VCF/3DStreetNumbers/Z.stl

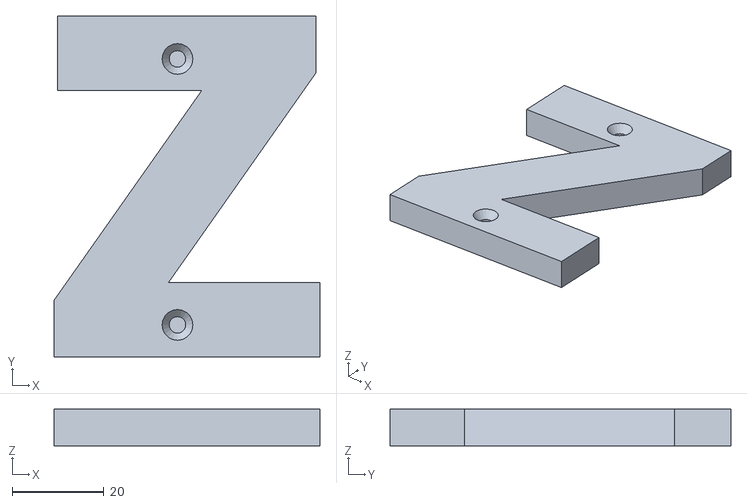
[picture p16: CAD file, 2019-05-19]
Z.stl
57.9 x 74.4 x 8.00
