VCF/3DStreetNumbers/O.stl

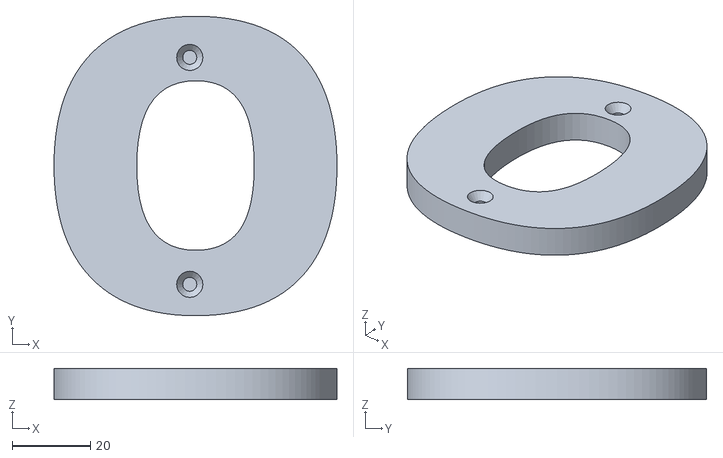
[picture p17: CAD file, 2019-05-19]
O.stl
72.3 x 76.5 x 8.00
