VCF/3DStreetNumbers/U.stl

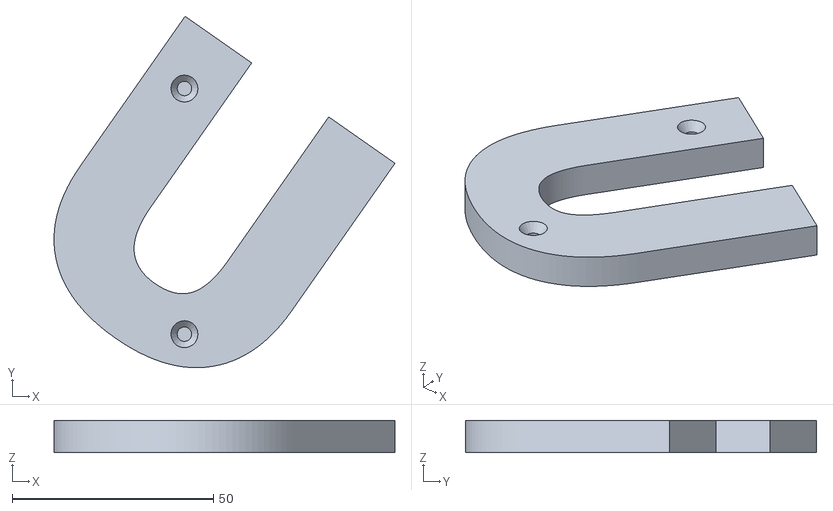
[picture p18: CAD file, 2019-05-19]
U.stl
84.7 x 87.3 x 8.00
