VCF/3DStreetNumbers/num.stl

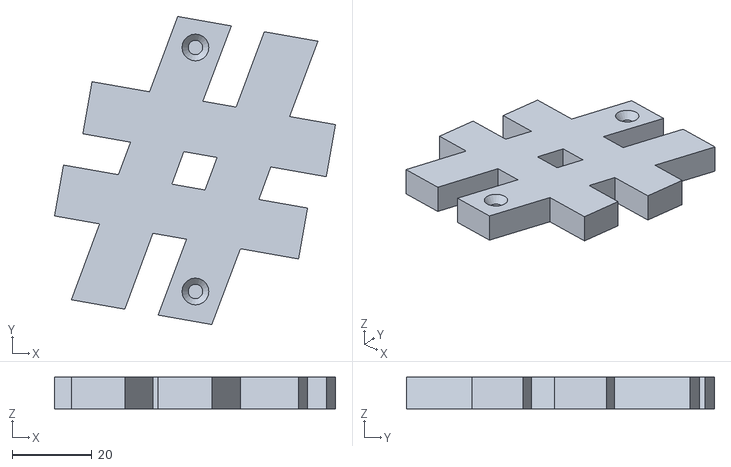
[picture p19: CAD file, 2019-05-19]
num.stl
70.3 x 77.0 x 8.00
