VCF/3DStreetNumbers/dot.stl

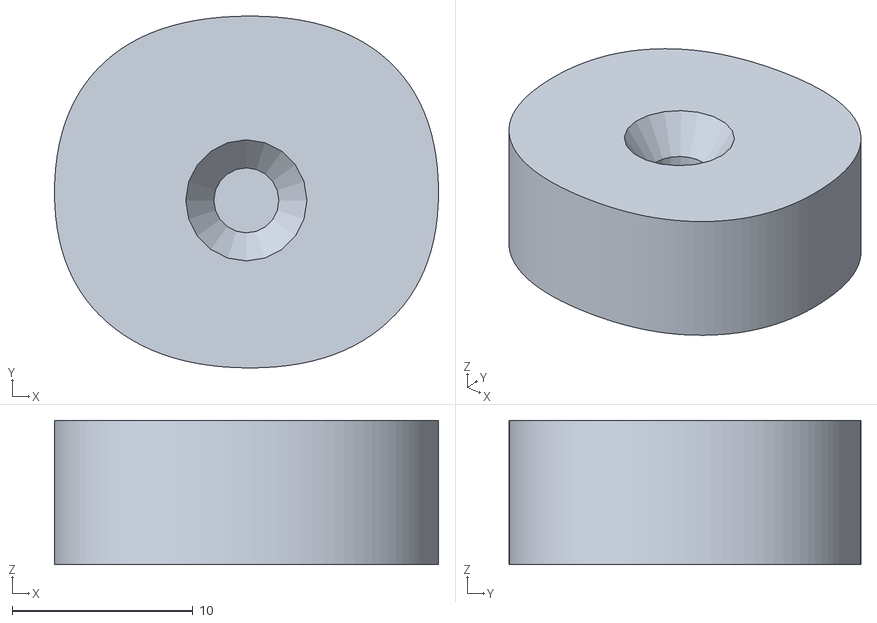
[picture p20: CAD file, 2019-05-18]
dot.stl
21.3 x 19.5 x 8.00
