VCF/3DStreetNumbers/F.stl

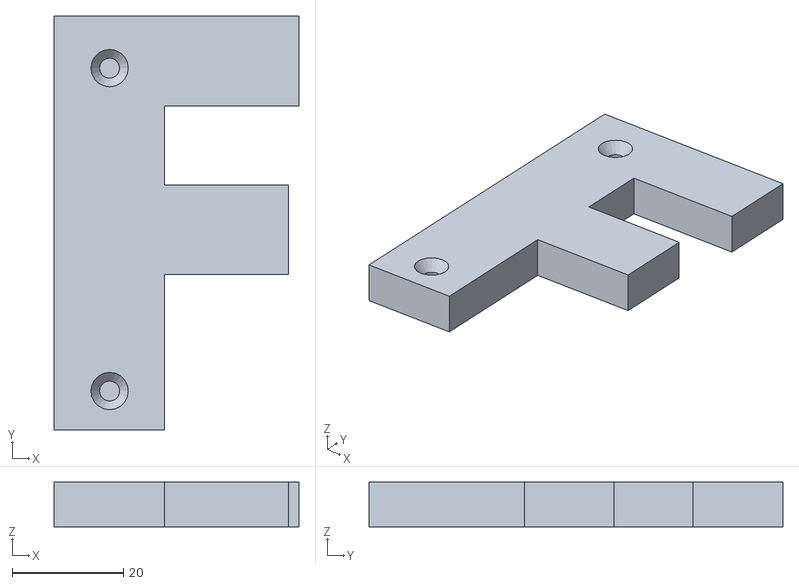
[picture p21: CAD file, 2019-05-18]
F.stl
44.0 x 74.4 x 8.00
