VCF/3DStreetNumbers/A.stl

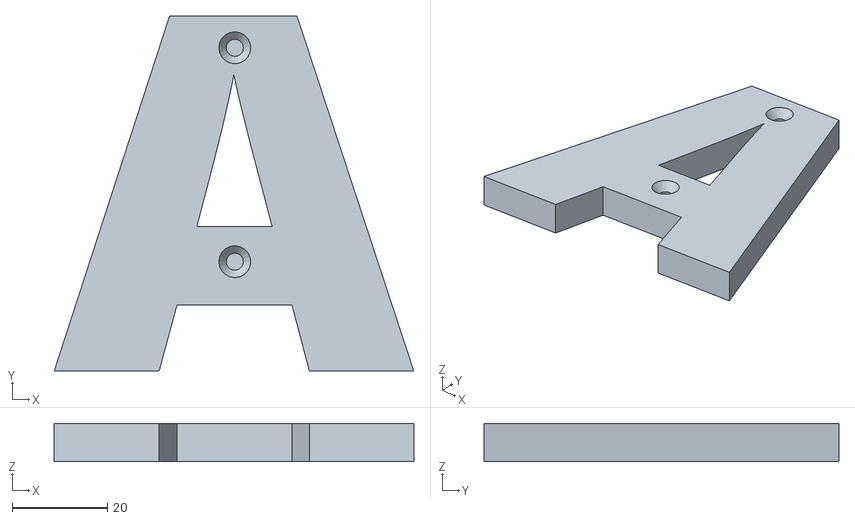
[picture p22: CAD file, 2019-05-18]
A.stl
75.7 x 74.7 x 8.00
