VCF/3DStreetNumbers/B.stl

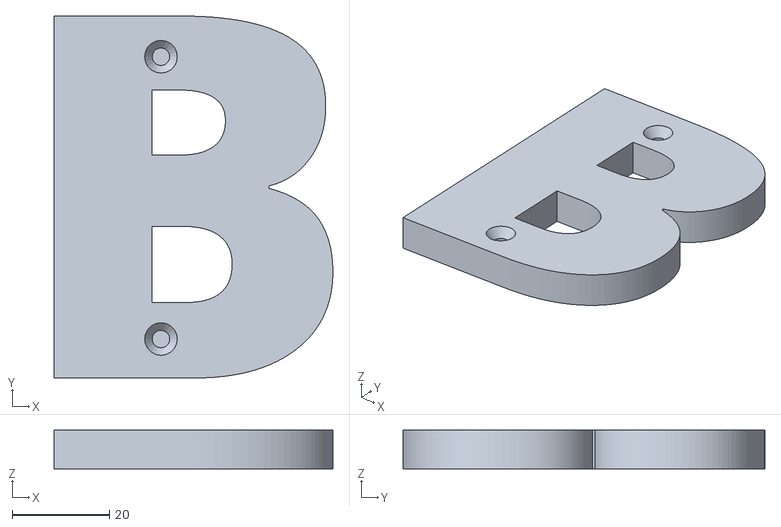
[picture p23: CAD file, 2019-05-18]
B.stl
57.3 x 74.4 x 8.00
