VCF/3DStreetNumbers/dash.stl

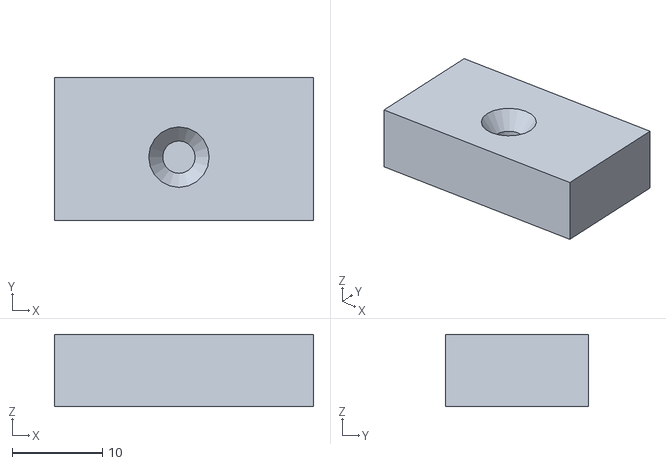
[picture p24: CAD file, 2019-05-18]
dash.stl
28.7 x 15.9 x 8.00
