VCF/3DStreetNumbers/J.stl

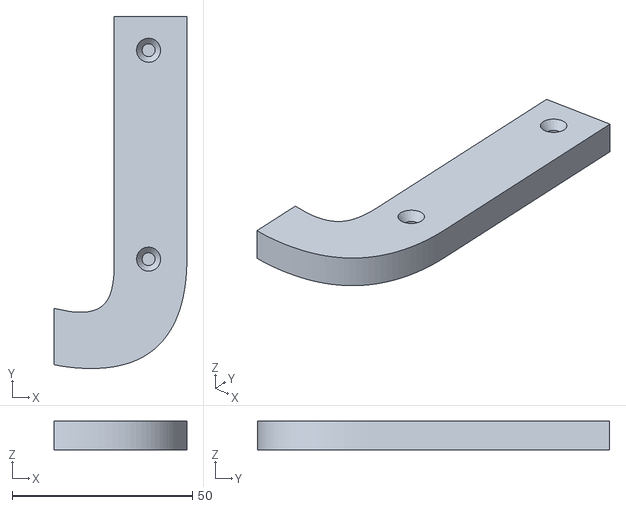
[picture p25: CAD file, 2019-05-18]
J.stl
36.9 x 97.7 x 8.00
