VCF/3DStreetNumbers/H.stl

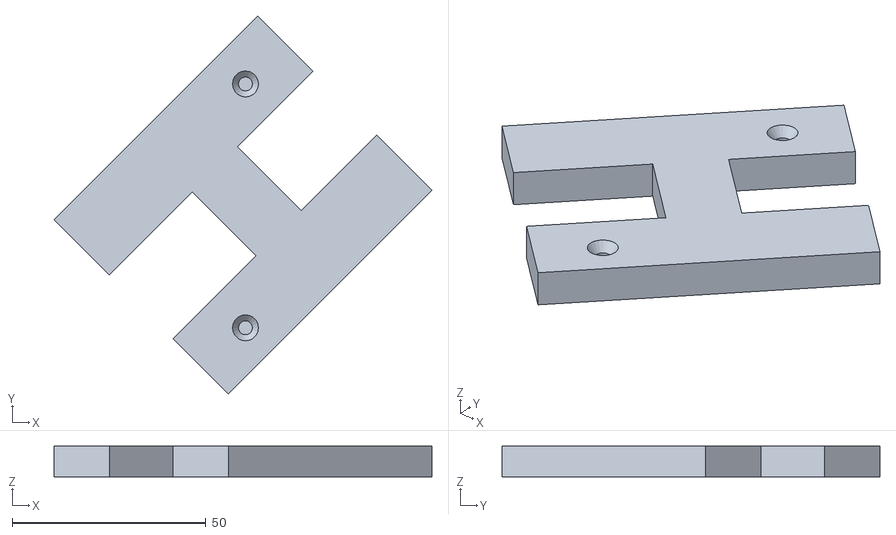
[picture p26: CAD file, 2019-05-18]
H.stl
97.7 x 97.7 x 8.00
