VCF/3DStreetNumbers/C.stl

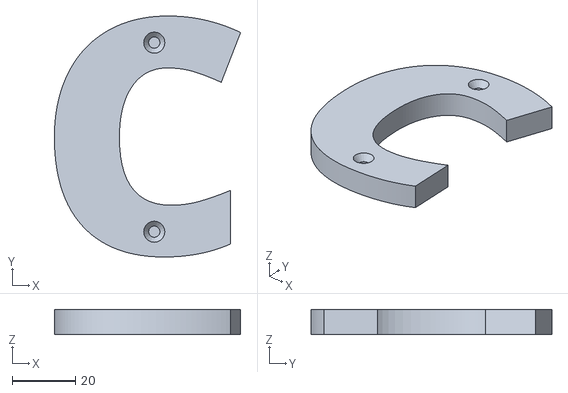
[picture p27: CAD file, 2019-05-18]
C.stl
59.1 x 76.5 x 8.00
