VCF/3DStreetNumbers/K.stl

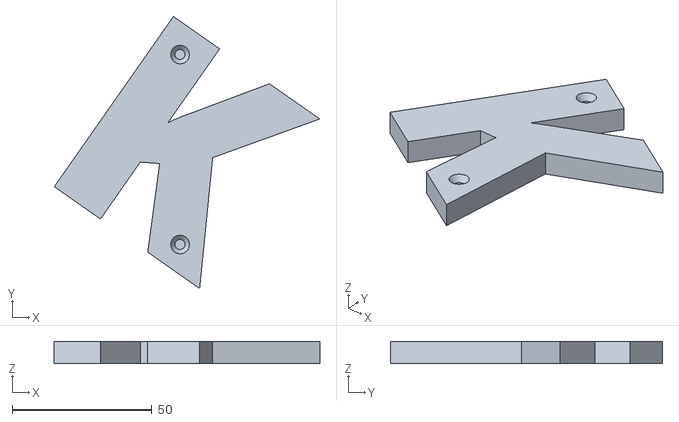
[picture p28: CAD file, 2019-05-18]
K.stl
95.0 x 97.4 x 8.00
