VCF/3DStreetNumbers/and.stl

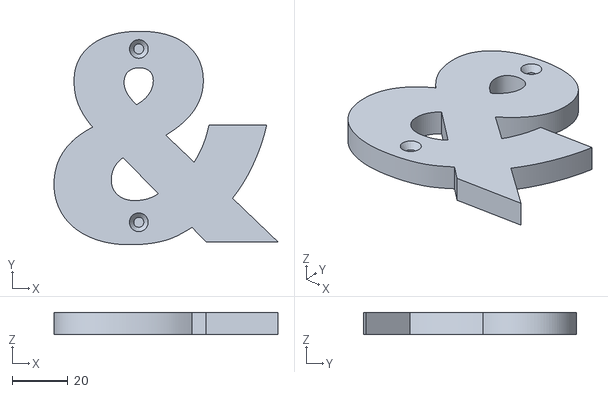
[picture p29: CAD file, 2019-05-18]
and.stl
80.1 x 76.4 x 8.00
