VCF/3DStreetNumbers/E.stl

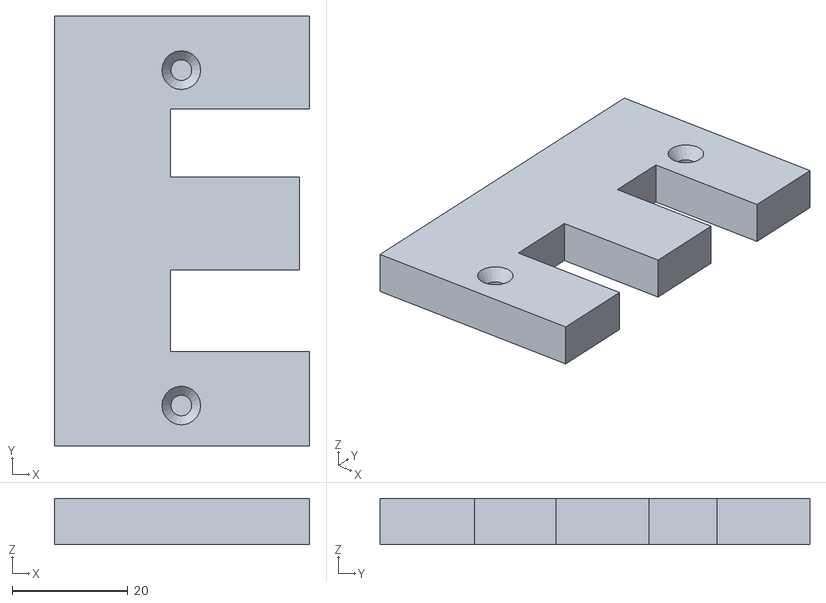
[picture p30: CAD file, 2019-05-18]
E.stl
44.2 x 74.4 x 8.00
