VCF/3DStreetNumbers/I.stl

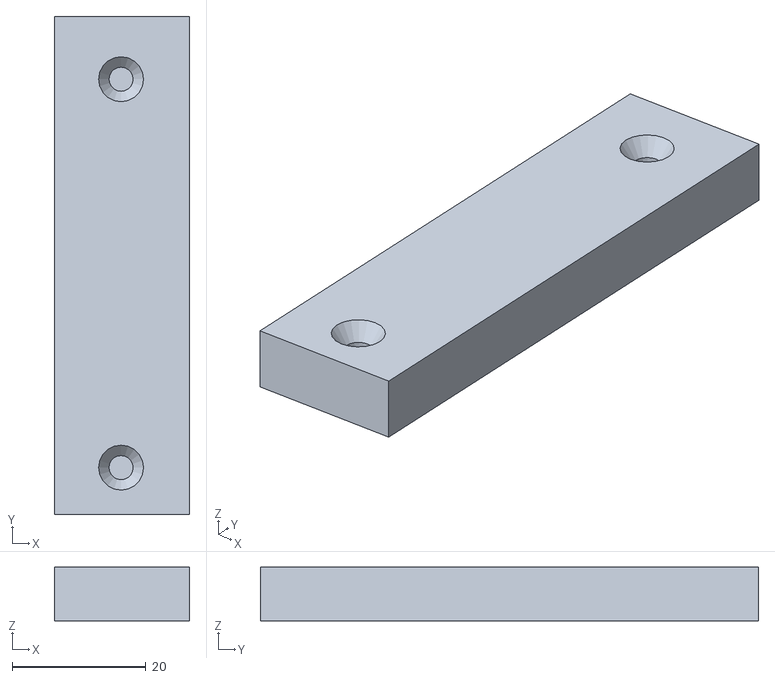
[picture p31: CAD file, 2019-05-18]
I.stl
20.2 x 74.4 x 8.00
