VCF/3DStreetNumbers/L.stl

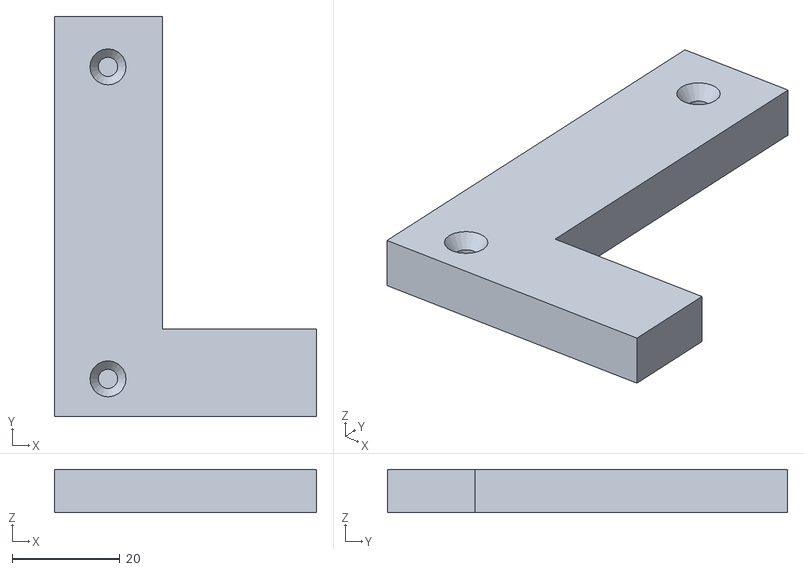
[picture p32: CAD file, 2019-05-18]
L.stl
48.7 x 74.4 x 8.00
