VCF/3DStreetNumbers/G.stl

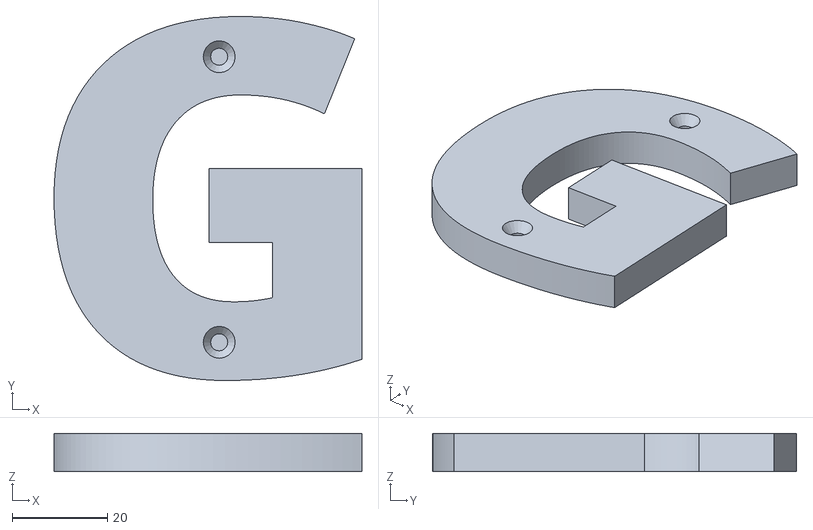
[picture p33: CAD file, 2019-05-18]
G.stl
64.7 x 76.5 x 8.00
