VCF/3DStreetNumbers/D.stl

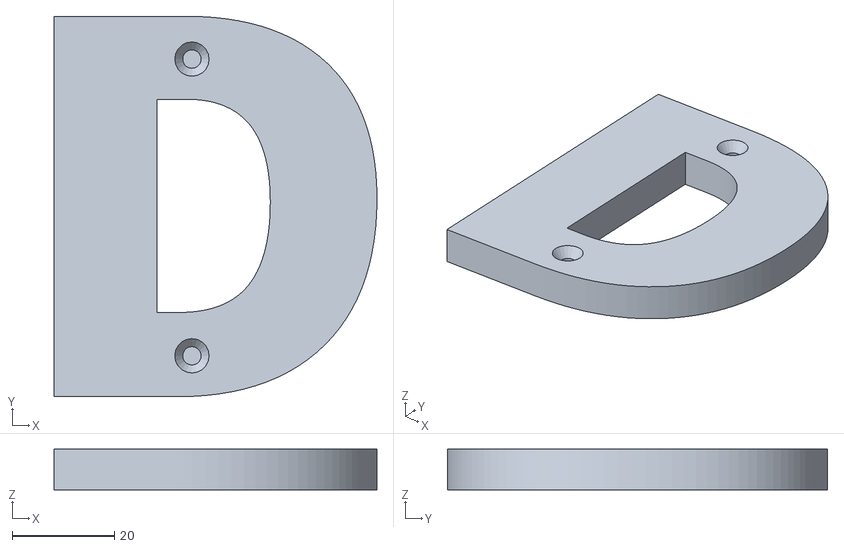
[picture p34: CAD file, 2019-05-18]
D.stl
63.1 x 74.4 x 8.00
