VCF/3DStreetNumbers/5.stl

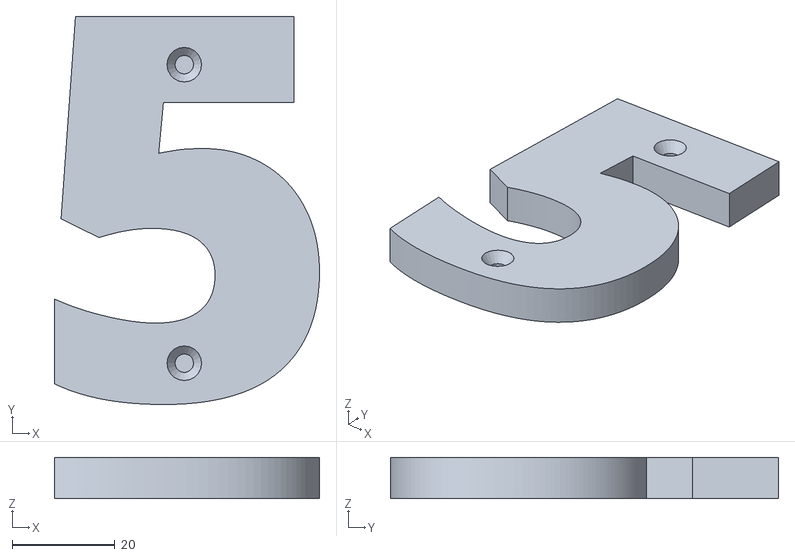
[picture p35: CAD file, 2019-05-18]
5.stl
51.5 x 75.4 x 8.00
