VCF/3DStreetNumbers/1.stl

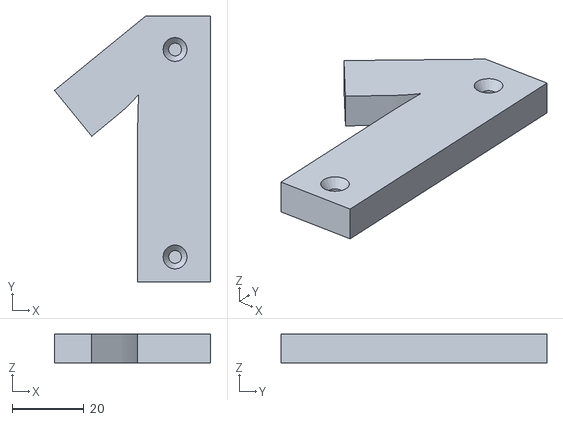
[picture p36: CAD file, 2019-05-18]
1.stl
43.6 x 74.4 x 8.00
