VCF/3DStreetNumbers/2.stl

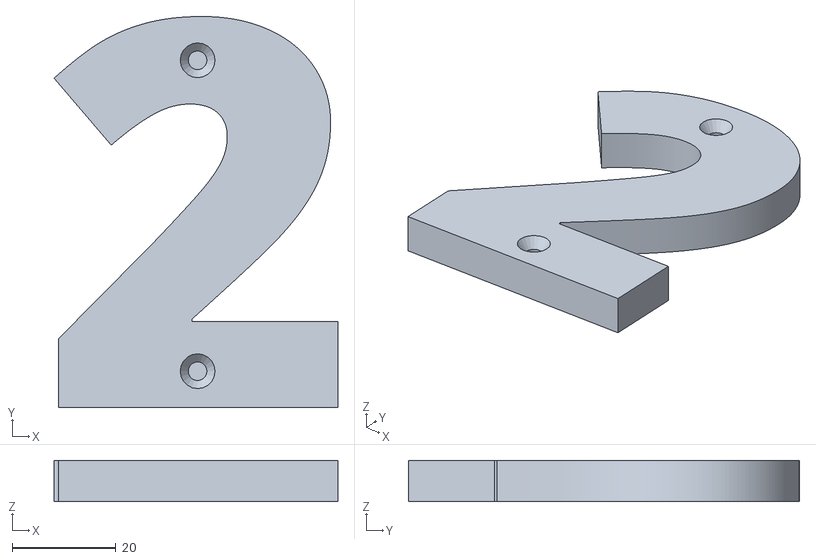
[picture p37: CAD file, 2019-05-18]
2.stl
54.8 x 75.5 x 8.00
