VCF/3DStreetNumbers/4.stl

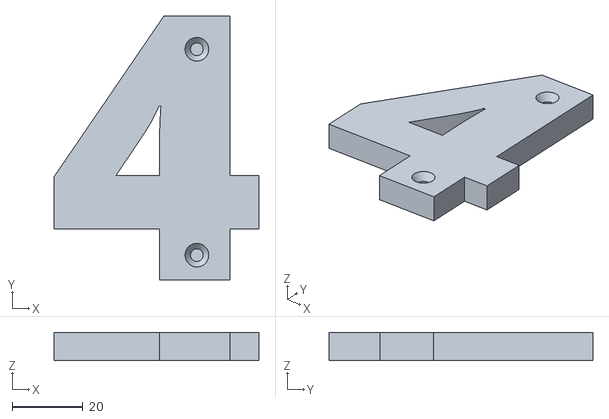
[picture p38: CAD file, 2019-05-18]
4.stl
57.7 x 74.4 x 8.00
