VCF/3DStreetNumbers/8.stl

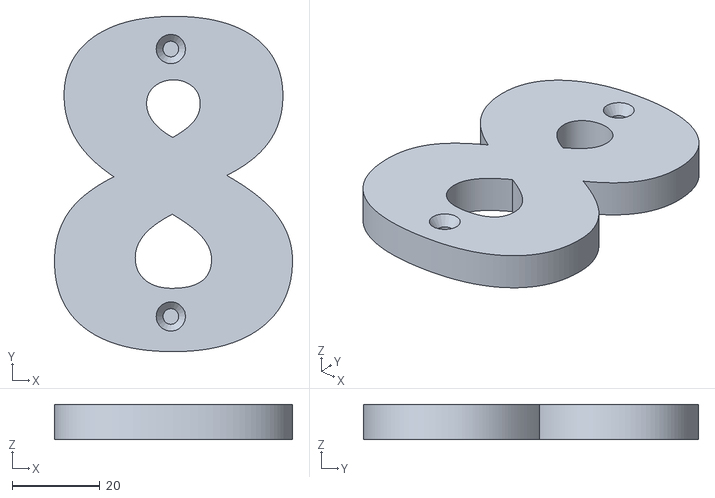
[picture p39: CAD file, 2019-05-18]
8.stl
54.3 x 76.5 x 8.00
