VCF/3DStreetNumbers/9.stl

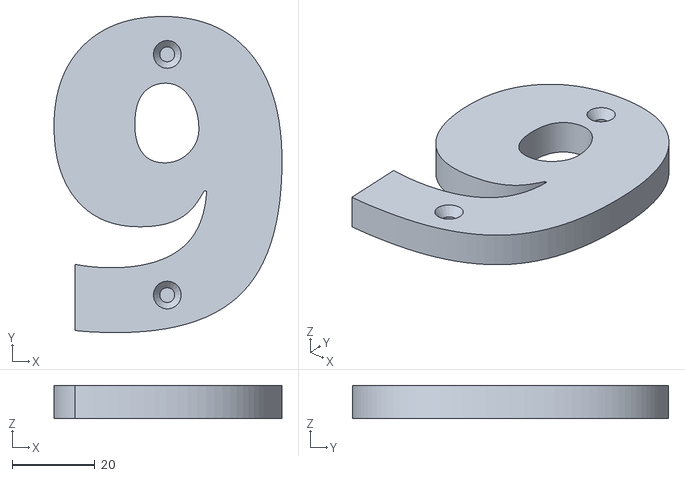
[picture p40: CAD file, 2019-05-18]
9.stl
54.9 x 76.2 x 8.00
