VCF/3DStreetNumbers/7.stl

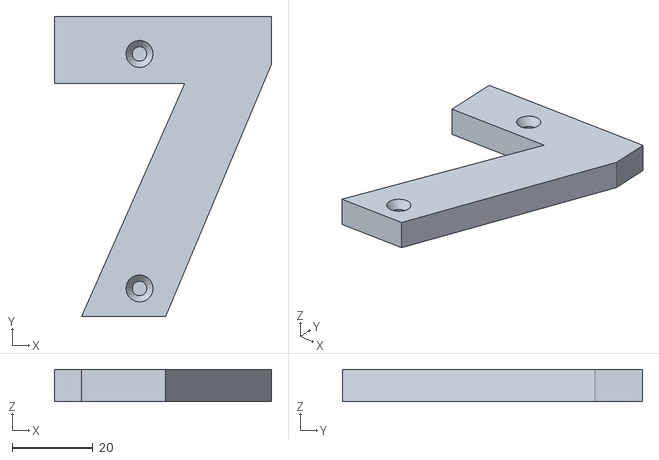
[picture p41: CAD file, 2019-05-18]
7.stl
53.7 x 74.3 x 8.00
