VCF/3DStreetNumbers/3.stl

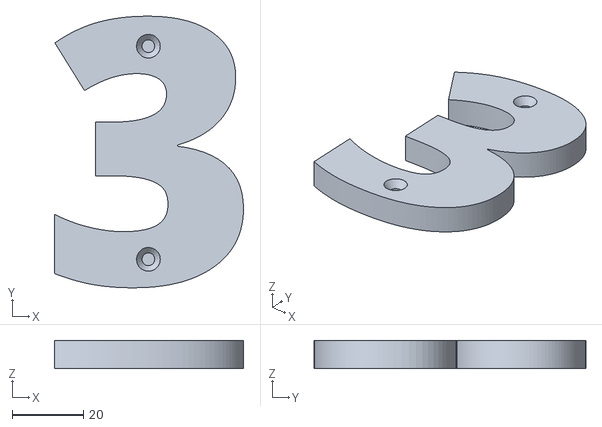
[picture p42: CAD file, 2019-05-18]
3.stl
53.2 x 76.5 x 8.00
